kc-GitHub/Wettersensor/Contrib/CCU/HB-UW-Sen-THPL_CCU-addon-src/www/config/img/devices/250/hb-uw-sen-thpl-o.png

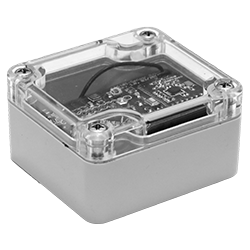
Contrib/CCU/HB-UW-Sen-THPL_CCU-addon-src/www/config/img/devices/250/hb-uw-sen-thpl-o.png
