kc-GitHub/Wettersensor/Images/CC1101-Sensor-Außen Platine_1.jpg

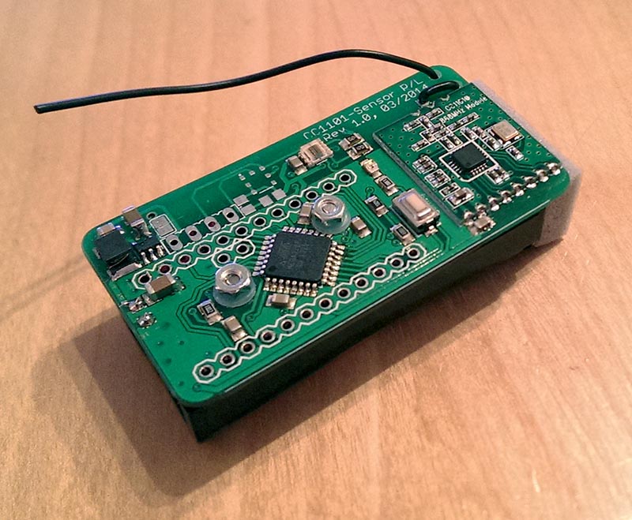
Images/CC1101-Sensor-Außen Platine_1.jpg
